mhnajafi/BeagleBone_Extension/Picture/DO/4.jpg

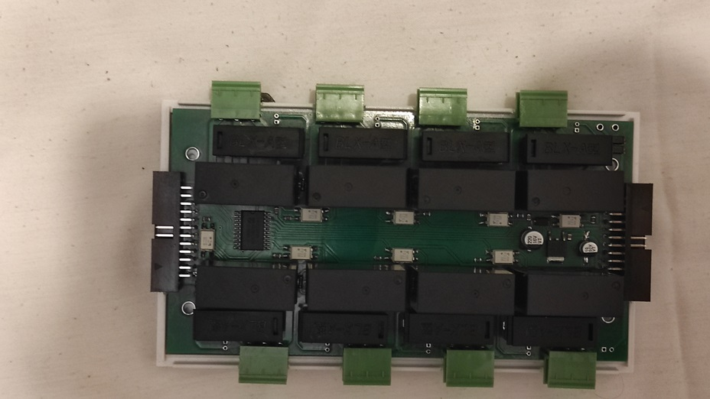
Picture/DO/4.jpg
