mhnajafi/BeagleBone_Extension/Picture/DO/5.jpg

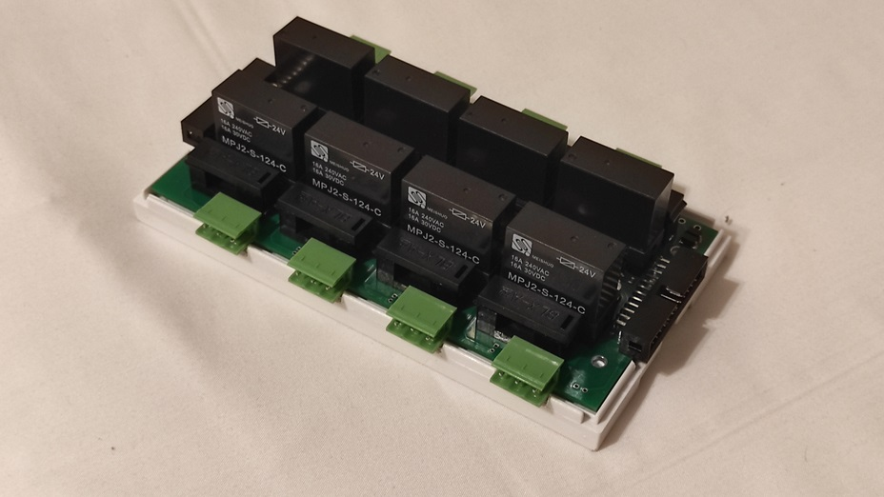
Picture/DO/5.jpg
