mhnajafi/BeagleBone_Extension/Picture/DO/6.jpg

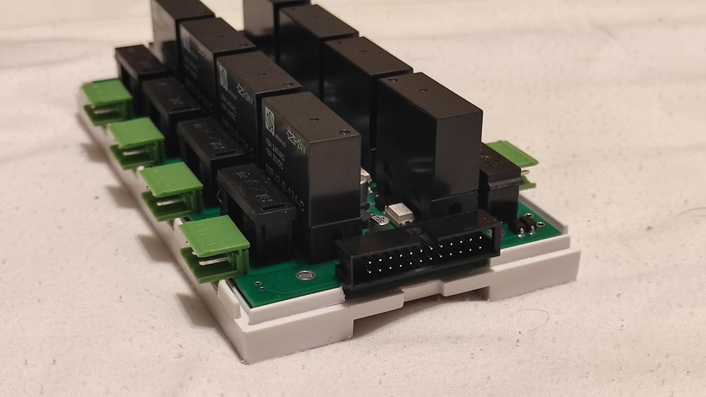
Picture/DO/6.jpg
