mhnajafi/BeagleBone_Extension/Picture/DO/7.jpg

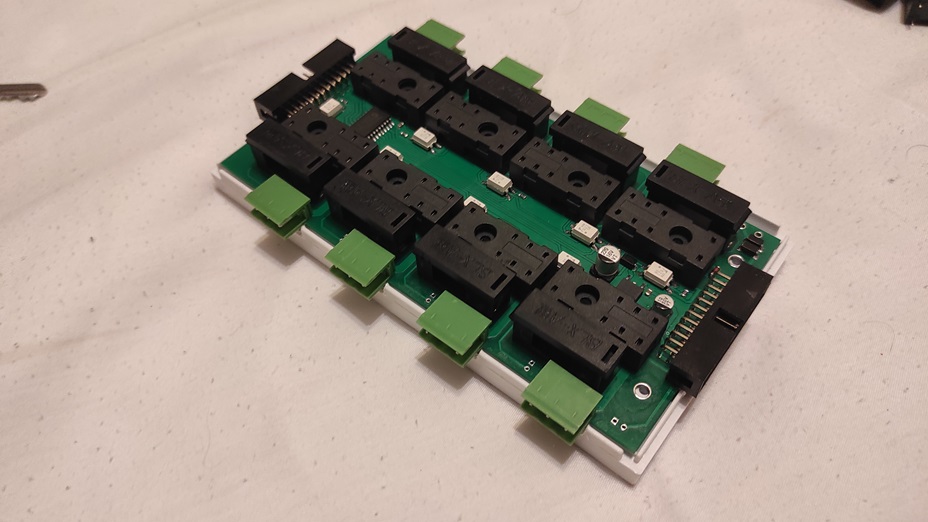
Picture/DO/7.jpg
