mhnajafi/BeagleBone_Extension/Picture/DO/8.jpg

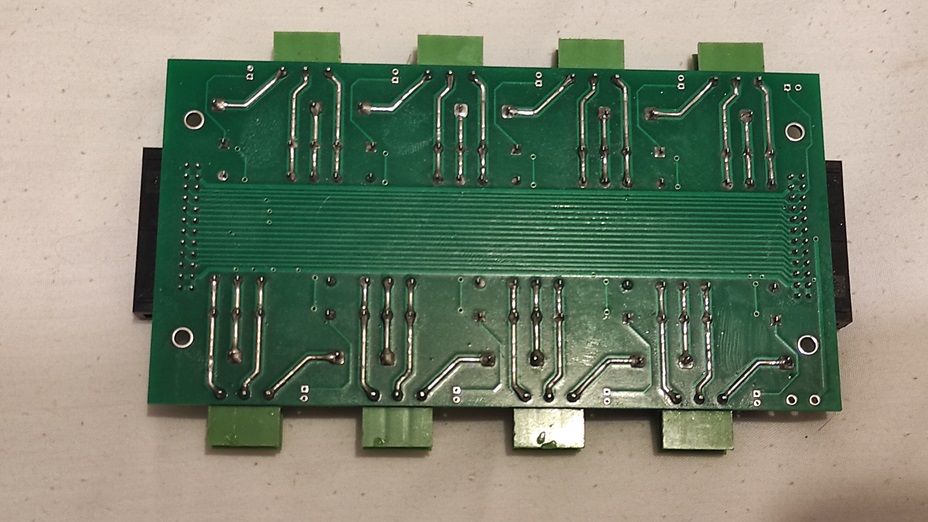
Picture/DO/8.jpg
