mhnajafi/BeagleBone_Extension/Picture/DO/10.jpg

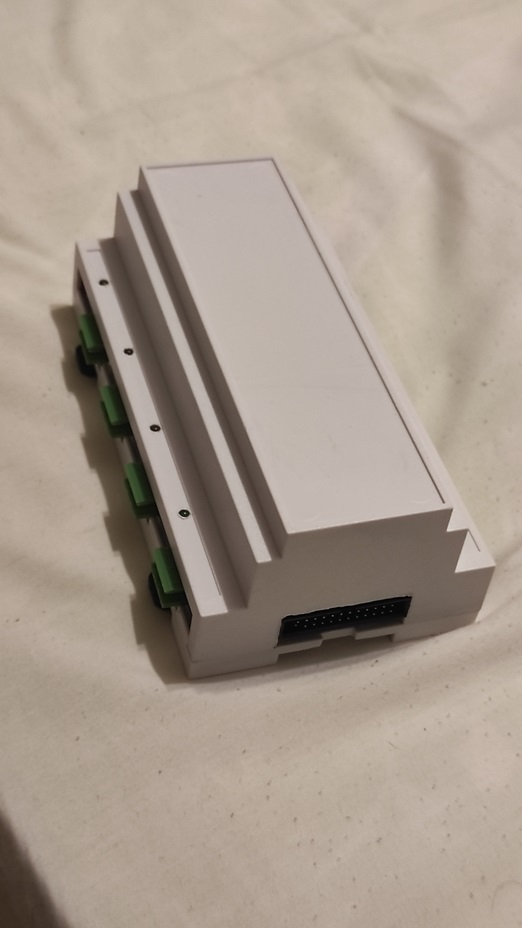
Picture/DO/10.jpg
