mhnajafi/BeagleBone_Extension/Picture/Main/1.jpg

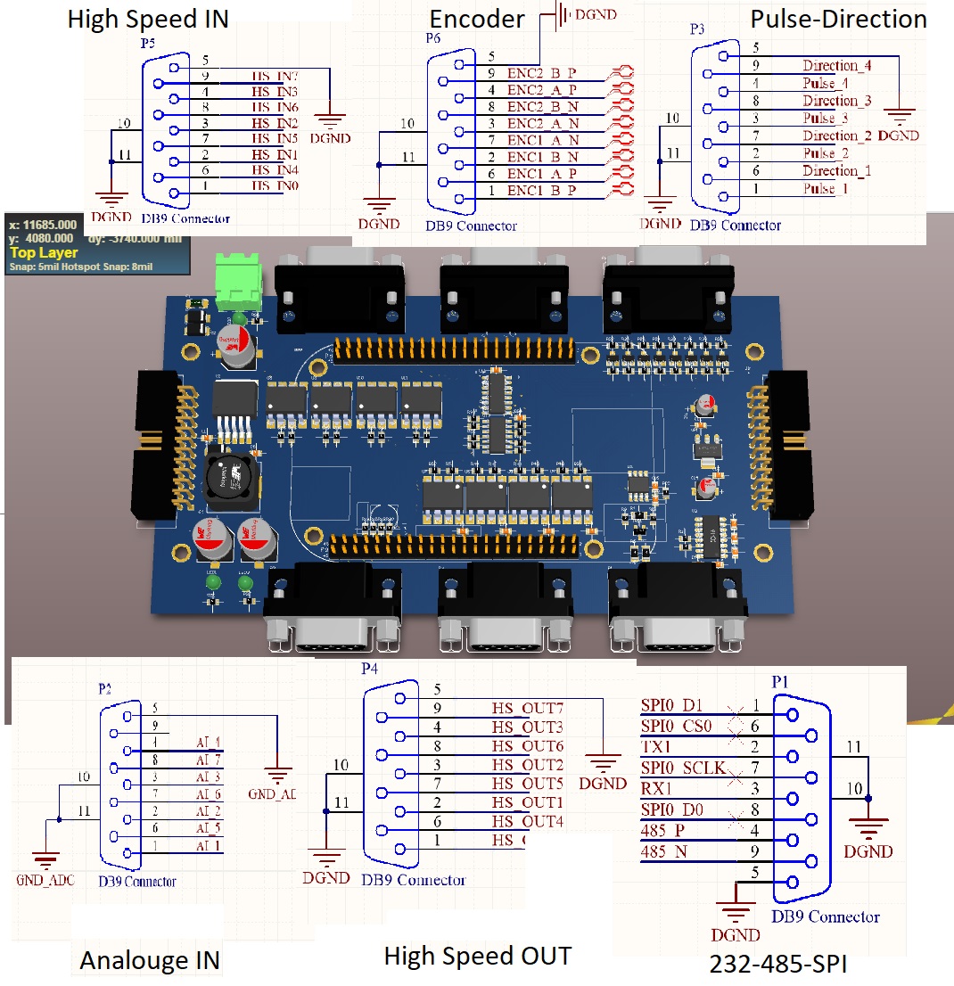
Picture/Main/1.jpg
