mhnajafi/BeagleBone_Extension/Picture/Main/4.png

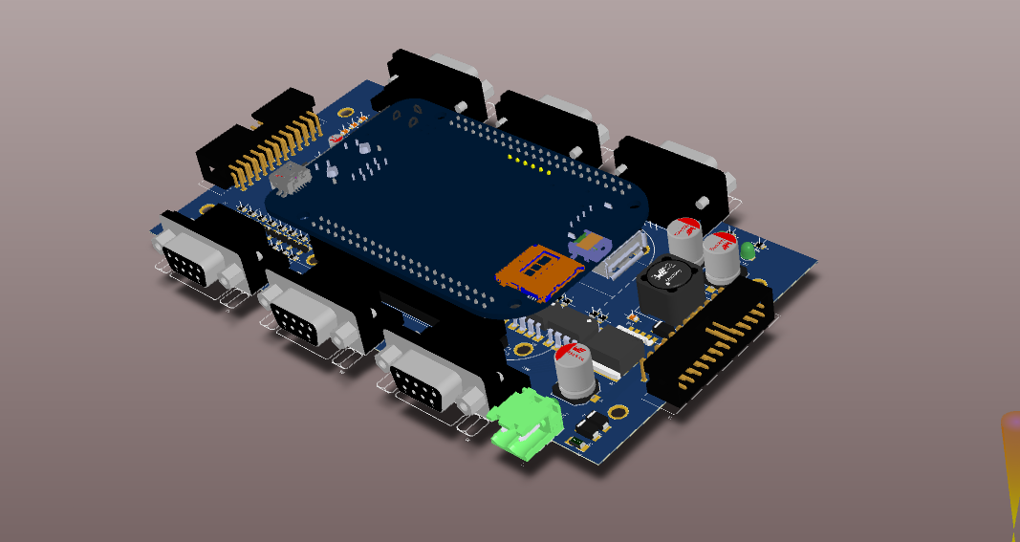
Picture/Main/4.png
