mhnajafi/BeagleBone_Extension/Picture/Main/5.png

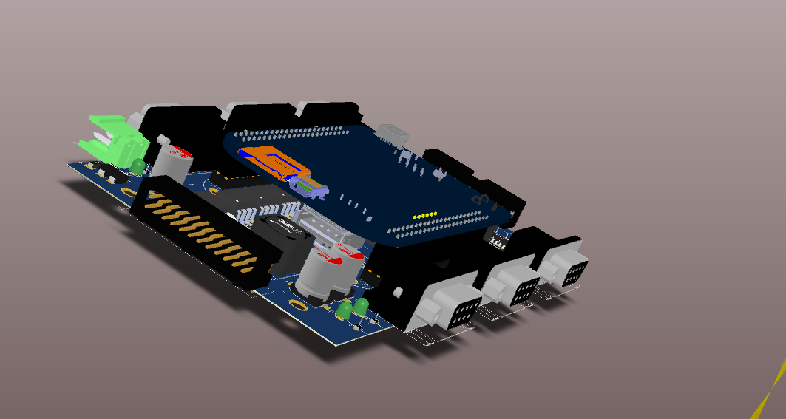
Picture/Main/5.png
