mhnajafi/BeagleBone_Extension/Picture/Main/6.png

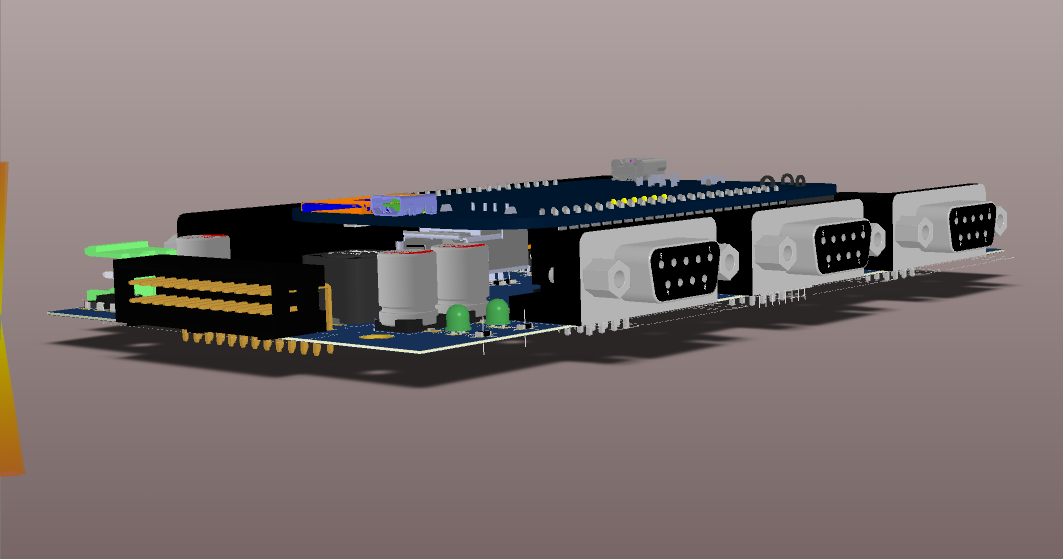
Picture/Main/6.png
