mhnajafi/BeagleBone_Extension/Picture/Main/7.png

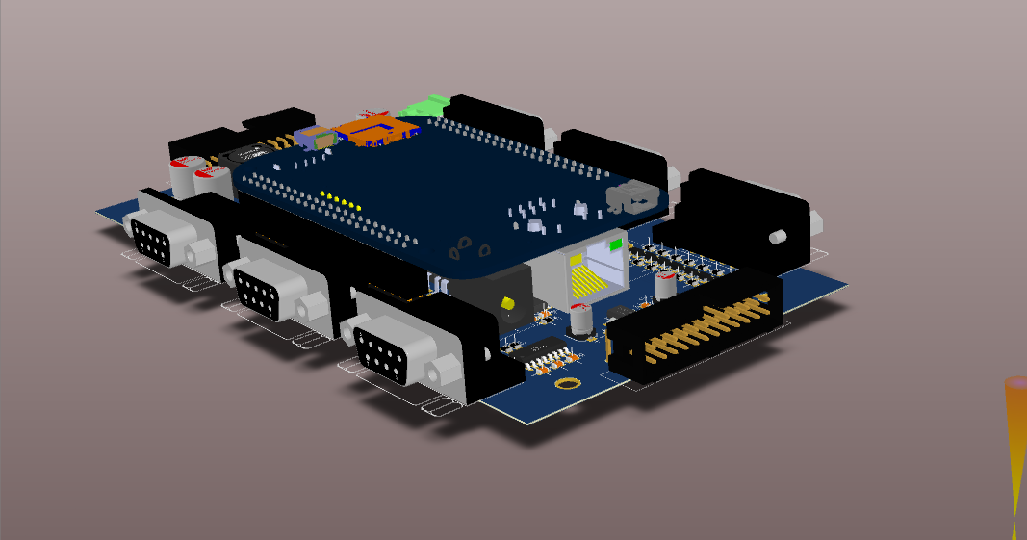
Picture/Main/7.png
