mhnajafi/BeagleBone_Extension/Picture/Main/8.png

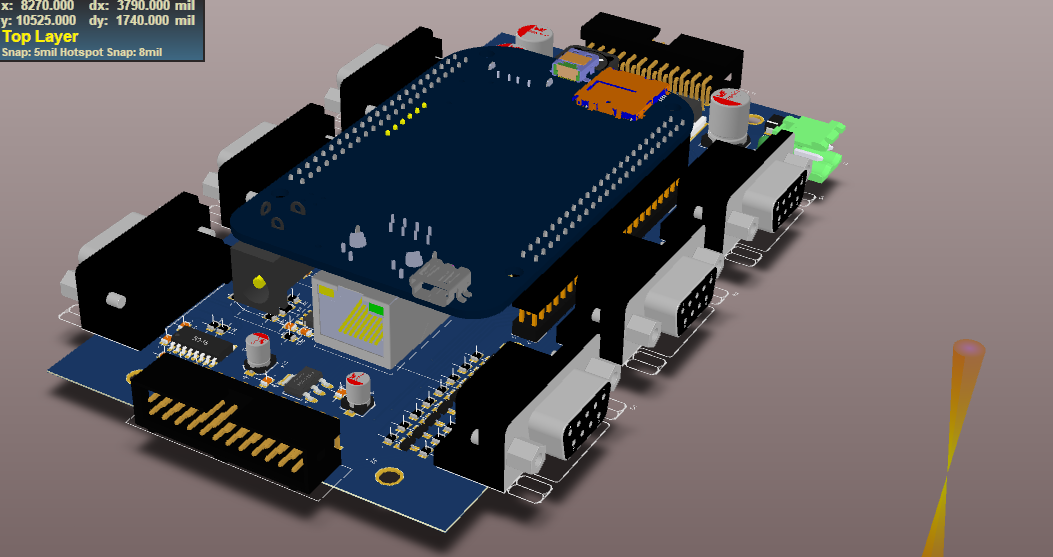
Picture/Main/8.png
